morozovsky/countingClock/Software/counting_clock/constants.h

const char* secret_ssid = "your_wifi_network_name"; // case-sensitive
const char* secret_password = "your_wifi_password"; // case-sensitive
const int gmt_offset_hours = -8; // set for your time zone
const int use_daylight_savings = 1;

uint8_t target_second = 0;
uint8_t target_minute = 0;
uint8_t target_hour = 0;
uint8_t target_day = 3;
uint8_t target_month = 11;
uint8_t target_year = 2020;
